liamlacey/Turnado-Hardware-MIDI-Controller/Circuit_Design/TurnadoHardwareMidiController/TurnadoHardwareMidiController.sch

## KiCad design Circuit_Design/TurnadoHardwareMidiController/TurnadoHardwareMidiController.sch (2018-10-14)

Schematic: TurnadoHardwareMidiController.sch

Parts:
R1: 100
SW1, SW6, SW7: Rotary_Encoder
SW2, SW3, SW8, SW10, SW11, SW12, SW13, SW14, SW15, SW16: Rotary_Encoder_Switch
SW4, SW5, SW9: SW_Push
U1, U2, U3, U4, U5, U7, U8, U10, U11: JOYSTICK_MODULE
U6: Teensy3.6
U9: CR2013-MI2120

Notes on the sheet:
SW1 - LCD Enc 2 SW2 - LCD Enc 1 SW3 - Dictator Enc SW4 - Randomise Button SW5 - Preset Up Button SW6 - Mix Encoder SW7 - LCD Enc 3 SW8 - Knob Controlller Enc 5 SW9 - Preset Down Button SW10 - Knob Controlller Enc 6 SW11 - Knob Controlller Enc 7 SW12 - Knob Controlller Enc 4 SW13 - Knob Controlller 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
U1 - Dictator Joystick U2 - Knob Controller Joystick 4 U3 - Knob Controller Joystick 3 U4 - Knob Controller Joystick 6 U5 - Knob Controller Joystick 5 U6 - Teensy 3.6 Microcontroller U7 - Knob Controller Joystick 7 U8 - Knob Controller Joystick 1 U9 - LCD U10 - Knob Controller Joystick 2 U11 - Knob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
